ergonomic-keyboard/wip/mechanisms/mechansims1.md

1 left half, 2 right half, Magenta — the keyboard halves (two wings)
Black — left rod with center hinge eye through belly-screen axis
Red — the rod passing through the eye and attachment to right eye.

3, the hinge center. 

4, 5, the angled rods, so that when it is folded close, the 2 keyboard halves can fold flat without the 2 closest edges running into eachother before the outer edges have reached eachother. 

Green — the folding adjustment rod, 
6. green the adjustment turnbuckle cilinder
7. The quick-release magnet
8. The attachment of the adjustment turnbuckle rod to the right half hinge rod.

9. The attachment of the adjustment turnbuckle rod to the left half hinge rod.

Yellow numbers — component labels (2, 3, 4, 5, 6, 8, 9)
